AlmCoding/micro-amps/images/pcb.png

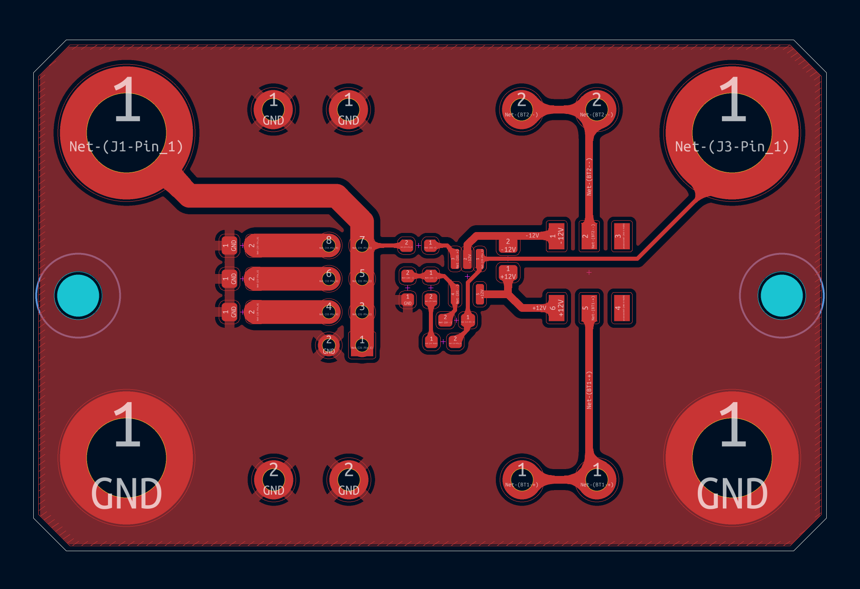
images/pcb.png
