AlmCoding/micro-amps/images/pcb_front-min_crop.jpg

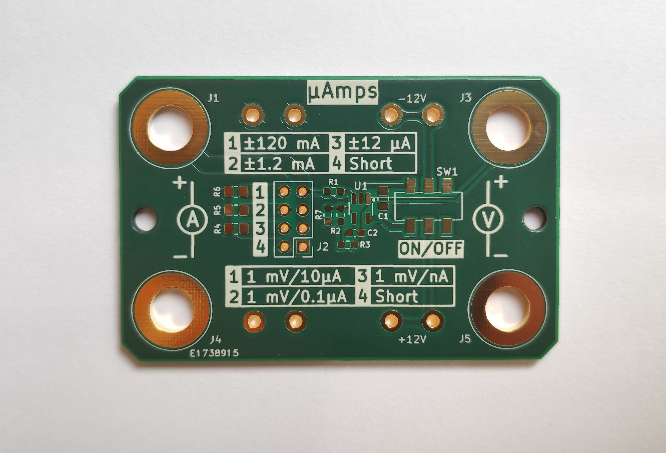
images/pcb_front-min_crop.jpg
